1stage/Aquarius-MiniExpander-1-1-0/images/IMG_6343.JPEG

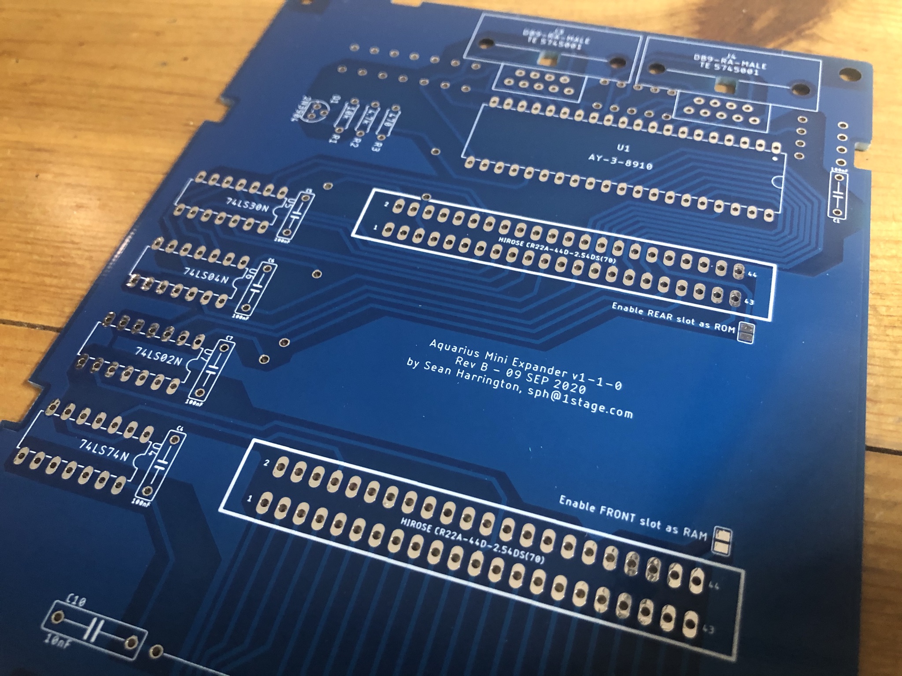
images/IMG_6343.JPEG
