1stage/Aquarius-MiniExpander-1-1-0/images/IMG_6344.JPEG

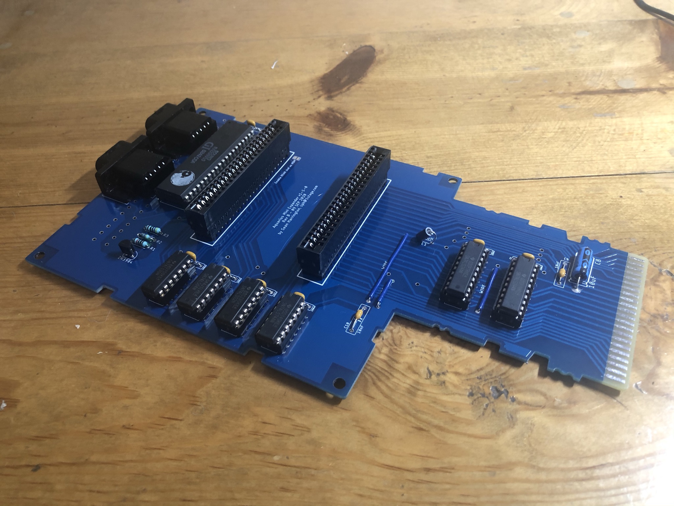
images/IMG_6344.JPEG
