1stage/Aquarius-MiniExpander-1-1-0/images/IMG_6345.JPEG

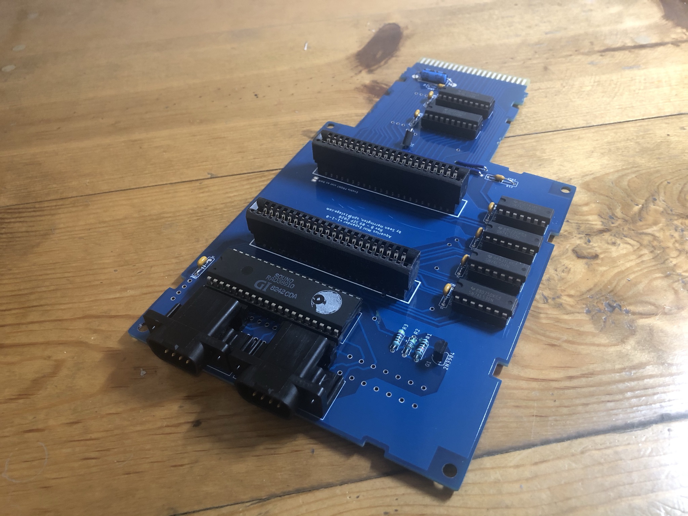
images/IMG_6345.JPEG
